GrantMaiden/ContactlessPiPoweredDrumkit/embedded/docs/pdf/files.tex

\doxysubsection{File List}
Here is a list of all documented files with brief descriptions\+:\begin{DoxyCompactList}
\item\contentsline{section}{include/\mbox{\hyperlink{btb__main_8h_source}{btb\+\_\+main.\+h}} }{\pageref{btb__main_8h_source}}{}
\item\contentsline{section}{include/\mbox{\hyperlink{controller_8h_source}{controller.\+h}} }{\pageref{controller_8h_source}}{}
\item\contentsline{section}{include/\mbox{\hyperlink{CppThread_8h_source}{Cpp\+Thread.\+h}} }{\pageref{CppThread_8h_source}}{}
\item\contentsline{section}{include/\mbox{\hyperlink{CppTimer_8h_source}{Cpp\+Timer.\+h}} }{\pageref{CppTimer_8h_source}}{}
\item\contentsline{section}{include/\mbox{\hyperlink{defines_8h_source}{defines.\+h}} }{\pageref{defines_8h_source}}{}
\item\contentsline{section}{include/\mbox{\hyperlink{gpio__controller_8h_source}{gpio\+\_\+controller.\+h}} }{\pageref{gpio__controller_8h_source}}{}
\item\contentsline{section}{include/\mbox{\hyperlink{led_8h_source}{led.\+h}} }{\pageref{led_8h_source}}{}
\item\contentsline{section}{include/\mbox{\hyperlink{platform_8h_source}{platform.\+h}} }{\pageref{platform_8h_source}}{}
\item\contentsline{section}{include/\mbox{\hyperlink{ranging_8h_source}{ranging.\+h}} }{\pageref{ranging_8h_source}}{}
\item\contentsline{section}{include/\mbox{\hyperlink{sound_8h_source}{sound.\+h}} }{\pageref{sound_8h_source}}{}
\item\contentsline{section}{include/\mbox{\hyperlink{types_8h_source}{types.\+h}} }{\pageref{types_8h_source}}{}
\item\contentsline{section}{include/\mbox{\hyperlink{VL53L4CD__api_8h_source}{VL53\+L4\+CD\+\_\+api.\+h}} }{\pageref{VL53L4CD__api_8h_source}}{}
\end{DoxyCompactList}
