GrantMaiden/ContactlessPiPoweredDrumkit/embedded/docs/pdf/hierarchy.tex

\doxysubsection{Class Hierarchy}
This inheritance list is sorted roughly, but not completely, alphabetically\+:\begin{DoxyCompactList}
\item \contentsline{section}{Cpp\+Thread}{\pageref{classCppThread}}{}
\item \contentsline{section}{Cpp\+Timer}{\pageref{classCppTimer}}{}
\begin{DoxyCompactList}
\item \contentsline{section}{Led\+Control}{\pageref{classLedControl}}{}
\end{DoxyCompactList}
\item \contentsline{section}{Gpio\+Controller}{\pageref{classGpioController}}{}
\item \contentsline{section}{Platform\+VL53l4\+CD}{\pageref{classPlatformVL53l4CD}}{}
\item \contentsline{section}{sensor\+Hit}{\pageref{structsensorHit}}{}
\item \contentsline{section}{sensor\+Values}{\pageref{structsensorValues}}{}
\item \contentsline{section}{Sound}{\pageref{classSound}}{}
\item \contentsline{section}{VL53\+L4\+CD}{\pageref{classVL53L4CD}}{}
\begin{DoxyCompactList}
\item \contentsline{section}{Controller}{\pageref{classController}}{}
\end{DoxyCompactList}
\item \contentsline{section}{VL53\+L4\+CD\+\_\+\+API}{\pageref{classVL53L4CD__API}}{}
\item \contentsline{section}{VL53\+L4\+CD\+\_\+\+Linux\+Dev}{\pageref{structVL53L4CD__LinuxDev}}{}
\item \contentsline{section}{VL53\+L4\+CD\+\_\+\+Results\+Data\+\_\+t}{\pageref{structVL53L4CD__ResultsData__t}}{}
\item \contentsline{section}{VL53\+L4\+CD\+\_\+\+Version\+\_\+t}{\pageref{structVL53L4CD__Version__t}}{}
\end{DoxyCompactList}
