GrantMaiden/ContactlessPiPoweredDrumkit/embedded/docs/pdf/structsensorHit.tex

\hypertarget{structsensorHit}{}\doxysubsection{sensor\+Hit Struct Reference}
\label{structsensorHit}\index{sensorHit@{sensorHit}}

{\ttfamily \#include $<$controller.\+h$>$}

\doxysubsubsection{Detailed Description}
sensor\+Value structure contains status and distance value of a sensor 

The documentation for this struct was generated from the following file\+:\begin{DoxyCompactItemize}
\item 
include/controller.\+h\end{DoxyCompactItemize}
