GrantMaiden/ContactlessPiPoweredDrumkit/embedded/docs/pdf/structsensorValues.tex

\hypertarget{structsensorValues}{}\doxysubsection{sensor\+Values Struct Reference}
\label{structsensorValues}\index{sensorValues@{sensorValues}}

{\ttfamily \#include $<$defines.\+h$>$}

\doxysubsubsection{Detailed Description}
\mbox{\hyperlink{structsensorValues}{sensor\+Values}} structure contains status and distance value of a sensor 

The documentation for this struct was generated from the following file\+:\begin{DoxyCompactItemize}
\item 
include/defines.\+h\end{DoxyCompactItemize}
