GrantMaiden/ContactlessPiPoweredDrumkit/embedded/docs/pdf/ranging_8h_source.tex

\hypertarget{ranging_8h_source}{}\doxysubsection{ranging.\+h}
\label{ranging_8h_source}\index{include/ranging.h@{include/ranging.h}}

\begin{DoxyCode}{0}
\DoxyCodeLine{1 \textcolor{comment}{/****************************** Module Header ******************************\(\backslash\)}}
\DoxyCodeLine{2 \textcolor{comment}{Module Name:    ranging.h}}
\DoxyCodeLine{3 \textcolor{comment}{Project:        btb}}
\DoxyCodeLine{4 \textcolor{comment}{Author:         Lucas Zehner}}
\DoxyCodeLine{5 \textcolor{comment}{Description:    contains ranging definitions and headers}}
\DoxyCodeLine{6 \textcolor{comment}{\(\backslash\)***************************************************************************/}}
\DoxyCodeLine{7 \textcolor{preprocessor}{\#ifndef RANGING\_H}}
\DoxyCodeLine{8 \textcolor{preprocessor}{\#define RANGING\_H}}
\DoxyCodeLine{9 \textcolor{keyword}{class }\mbox{\hyperlink{classGpioController}{GpioController}};}
\DoxyCodeLine{10 }
\DoxyCodeLine{11 }
\DoxyCodeLine{12 \textcolor{preprocessor}{\#define VL53L4CD\_I2C\_FAST\_MODE\_PLUS}}
\DoxyCodeLine{13 \textcolor{comment}{// Includes}}
\DoxyCodeLine{14 \textcolor{keyword}{extern} \textcolor{stringliteral}{"{}C"{}} \{}
\DoxyCodeLine{15 }
\DoxyCodeLine{16 \}}
\DoxyCodeLine{17 \textcolor{preprocessor}{\#include "{}VL53L4CD\_api.h"{}}}
\DoxyCodeLine{18 \textcolor{preprocessor}{\#include "{}types.h"{}}}
\DoxyCodeLine{19 \textcolor{preprocessor}{\#include "{}platform.h"{}}}
\DoxyCodeLine{20 \textcolor{preprocessor}{\#include <pigpio.h>}}
\DoxyCodeLine{21 }
\DoxyCodeLine{22 \textcolor{comment}{// Defines}}
\DoxyCodeLine{23 \textcolor{preprocessor}{\#define I2C\_ADDRESS\_INIT    0x52}}
\DoxyCodeLine{24 \textcolor{preprocessor}{\#define D1\_I2C\_ADDRESS      0x52}}
\DoxyCodeLine{25 \textcolor{preprocessor}{\#define D2\_I2C\_ADDRESS      0x54}}
\DoxyCodeLine{26 \textcolor{preprocessor}{\#define D3\_I2C\_ADDRESS      0x56}}
\DoxyCodeLine{27 \textcolor{preprocessor}{\#define D4\_I2C\_ADDRESS      0x58}}
\DoxyCodeLine{28 \textcolor{preprocessor}{\#define D5\_I2C\_ADDRESS      0x60}}
\DoxyCodeLine{29 \textcolor{preprocessor}{\#define D6\_I2C\_ADDRESS      0x62}}
\DoxyCodeLine{30 \textcolor{comment}{// Change these as desired}}
\DoxyCodeLine{31 \textcolor{preprocessor}{\#define RANGE\_TIMING\_MAX    10}}
\DoxyCodeLine{32 \textcolor{preprocessor}{\#define RANGING\_LIM\_LOW     10}}
\DoxyCodeLine{33 \textcolor{preprocessor}{\#define RANGING\_LIM\_HIGH    500}}
\DoxyCodeLine{34 }
\DoxyCodeLine{35 \textcolor{keyword}{using namespace }std;}
\DoxyCodeLine{36 \textcolor{keyword}{class }\mbox{\hyperlink{classVL53L4CD}{VL53L4CD}}}
\DoxyCodeLine{37 \{}
\DoxyCodeLine{38     \textcolor{keyword}{public}:}
\DoxyCodeLine{39         \textcolor{comment}{//Functions}}
\DoxyCodeLine{40 }
\DoxyCodeLine{44         \textcolor{keywordtype}{void} \mbox{\hyperlink{classVL53L4CD_aa50845e779bebe4d312e79ef1a14a62b}{rangingInit}}();}
\DoxyCodeLine{45 }
\DoxyCodeLine{49         \textcolor{keywordtype}{void} \mbox{\hyperlink{classVL53L4CD_a07ac79dcf2d0ba4c91df4fb0aea824f0}{rangingTestDistanceSensors}}();}
\DoxyCodeLine{50 }
\DoxyCodeLine{56         \mbox{\hyperlink{structsensorValues}{sensorValues}} \mbox{\hyperlink{classVL53L4CD_ad81309cbabd2f3a7f4eb1c26cd97a64d}{rangingGetData}}(sensorID sensor);}
\DoxyCodeLine{57 }
\DoxyCodeLine{63         \textcolor{keywordtype}{bool} \mbox{\hyperlink{classVL53L4CD_af33c4ab62ad9db0773ed3dadaa0257c5}{rangingCheckIfReady}}(sensorID sensor);}
\DoxyCodeLine{64 }
\DoxyCodeLine{72         \textcolor{keyword}{virtual} \textcolor{keywordtype}{void} \mbox{\hyperlink{classVL53L4CD_a149a2250aabe18254a50be683b9fbba5}{distanceDataReady}}(\mbox{\hyperlink{structsensorValues}{sensorValues}} sensVals, sensorID sensor) = 0;}
\DoxyCodeLine{73 }
\DoxyCodeLine{74     \textcolor{keyword}{private}:}
\DoxyCodeLine{75         \textcolor{comment}{// private global variables}}
\DoxyCodeLine{76         \mbox{\hyperlink{structVL53L4CD__LinuxDev}{VL53L4CD\_LinuxDev}} linuxDev1;}
\DoxyCodeLine{77         \mbox{\hyperlink{structVL53L4CD__LinuxDev}{Dev\_t}} i2cdev\_Sensor1 = \&linuxDev1;}
\DoxyCodeLine{78         \mbox{\hyperlink{structVL53L4CD__LinuxDev}{VL53L4CD\_LinuxDev}} linuxDev2;}
\DoxyCodeLine{79         \mbox{\hyperlink{structVL53L4CD__LinuxDev}{Dev\_t}} i2cdev\_Sensor2 = \&linuxDev2;}
\DoxyCodeLine{80         \mbox{\hyperlink{structVL53L4CD__LinuxDev}{VL53L4CD\_LinuxDev}} linuxDev3;}
\DoxyCodeLine{81         \mbox{\hyperlink{structVL53L4CD__LinuxDev}{Dev\_t}} i2cdev\_Sensor3 = \&linuxDev3;}
\DoxyCodeLine{82         \mbox{\hyperlink{structVL53L4CD__LinuxDev}{VL53L4CD\_LinuxDev}} linuxDev4;}
\DoxyCodeLine{83         \mbox{\hyperlink{structVL53L4CD__LinuxDev}{Dev\_t}} i2cdev\_Sensor4 = \&linuxDev4;}
\DoxyCodeLine{84         \mbox{\hyperlink{structVL53L4CD__LinuxDev}{VL53L4CD\_LinuxDev}} linuxDev5;}
\DoxyCodeLine{85         \mbox{\hyperlink{structVL53L4CD__LinuxDev}{Dev\_t}} i2cdev\_Sensor5 = \&linuxDev5;}
\DoxyCodeLine{86         \mbox{\hyperlink{structVL53L4CD__LinuxDev}{VL53L4CD\_LinuxDev}} linuxDev6;}
\DoxyCodeLine{87         \mbox{\hyperlink{structVL53L4CD__LinuxDev}{Dev\_t}} i2cdev\_Sensor6 = \&linuxDev6;}
\DoxyCodeLine{88 }
\DoxyCodeLine{89 }
\DoxyCodeLine{94         \textcolor{keywordtype}{void} rangingInitDistanceSensor(\textcolor{keywordtype}{int} \textcolor{keywordtype}{id}, \mbox{\hyperlink{structVL53L4CD__LinuxDev}{Dev\_t}} dev);}
\DoxyCodeLine{95 }
\DoxyCodeLine{101         \textcolor{keywordtype}{bool} rangingSetXshut(\textcolor{keywordtype}{int} \textcolor{keywordtype}{id});}
\DoxyCodeLine{102 }
\DoxyCodeLine{108         \textcolor{keywordtype}{void} rangingChangeAddress(\mbox{\hyperlink{structVL53L4CD__LinuxDev}{Dev\_t}} dev, \textcolor{keywordtype}{int} \textcolor{keywordtype}{id});}
\DoxyCodeLine{109 }
\DoxyCodeLine{113         \textcolor{keywordtype}{void} rangingPollingTestAll();}
\DoxyCodeLine{114 }
\DoxyCodeLine{115         \textcolor{keywordtype}{void} dataReadyISR(\textcolor{keywordtype}{int} gpio);}
\DoxyCodeLine{116 }
\DoxyCodeLine{117         \textcolor{keyword}{static} \textcolor{keywordtype}{void} rangingISRCallback(\textcolor{keywordtype}{int} gpio, \textcolor{keywordtype}{int}, uint32\_t, \textcolor{keywordtype}{void}* userdata) \{}
\DoxyCodeLine{118             ((\mbox{\hyperlink{classVL53L4CD}{VL53L4CD}}*)userdata)-\/>dataReadyISR(gpio);}
\DoxyCodeLine{119         \}}
\DoxyCodeLine{120 }
\DoxyCodeLine{121 }
\DoxyCodeLine{122 \};}
\DoxyCodeLine{123 }
\DoxyCodeLine{124 }
\DoxyCodeLine{125 \textcolor{preprocessor}{\#endif }\textcolor{comment}{// RANGING\_H}}
\DoxyCodeLine{126 }
\DoxyCodeLine{127 }
\DoxyCodeLine{128 }
\DoxyCodeLine{129 }
\DoxyCodeLine{130 }
\DoxyCodeLine{131 }
\DoxyCodeLine{132 }
\DoxyCodeLine{133 }
\DoxyCodeLine{134 }
\DoxyCodeLine{135 }

\end{DoxyCode}
