GrantMaiden/ContactlessPiPoweredDrumkit/embedded/docs/pdf/refman.tex

  % Handle batch mode
  % to overcome problems with too many open files
  \let\mypdfximage\pdfximage\def\pdfximage{\immediate\mypdfximage}
  % Set document class depending on configuration
  \documentclass[twoside]{article}
  %% moved from doxygen.sty due to workaround for LaTex 2019 version and unmaintained tabu package
  \usepackage{ifthen}
  \ifx\requestedLaTeXdate\undefined
    \usepackage{array}
  \else
    \usepackage{array}[=2016-10-06]
  \fi
  %%
  % Packages required by doxygen
  \usepackage{fixltx2e} % for \textsubscript
  \usepackage{doxygen}
  \usepackage{graphicx}
  \usepackage[utf8]{inputenc}
  \usepackage{makeidx}
  \PassOptionsToPackage{warn}{textcomp}
  \usepackage{textcomp}
  \usepackage[nointegrals]{wasysym}
  \usepackage{ifxetex}
  % NLS support packages
  % Define default fonts
  % Font selection
  \usepackage[T1]{fontenc}
  % set main and monospaced font
  \usepackage[scaled=.90]{helvet}
\usepackage{courier}
\renewcommand{\familydefault}{\sfdefault}
  \usepackage{sectsty}
  \allsectionsfont{%
    \fontseries{bc}\selectfont%
    \color{darkgray}%
  }
  \renewcommand{\DoxyLabelFont}{%
    \fontseries{bc}\selectfont%
    \color{darkgray}%
  }
  \newcommand{\+}{\discretionary{\mbox{\scriptsize$\hookleftarrow$}}{}{}}
   % Arguments of doxygenemoji:
   % 1) ':<text>:' form of the emoji, already LaTeX-escaped
   % 2) file with the name of the emoji without the .png extension
   % in case image exist use this otherwise use the ':<text>:' form
   \newcommand{\doxygenemoji}[2]{%
     \IfFileExists{./#2.png}{\raisebox{-0.1em}{}}{#1}%
   }
  % Page & text layout
  \usepackage{geometry}
  \geometry{%
    a4paper,%
    top=2.5cm,%
    bottom=2.5cm,%
    left=2.5cm,%
    right=2.5cm%
  }
  % Allow a bit of overflow to go unnoticed by other means
  \tolerance=750
  \hfuzz=15pt
  \hbadness=750
  \setlength{\emergencystretch}{15pt}
  \setlength{\parindent}{0cm}
  \newcommand{\doxynormalparskip}{\setlength{\parskip}{3ex plus 2ex minus 2ex}}
  \newcommand{\doxytocparskip}{\setlength{\parskip}{1ex plus 0ex minus 0ex}}
  \doxynormalparskip
  % Redefine paragraph/subparagraph environments, using sectsty fonts
  \makeatletter
  \renewcommand{\paragraph}{%
    \@startsection{paragraph}{4}{0ex}{-1.0ex}{1.0ex}{%
      \normalfont\normalsize\bfseries\SS@parafont%
    }%
  }
  \renewcommand{\subparagraph}{%
    \@startsection{subparagraph}{5}{0ex}{-1.0ex}{1.0ex}{%
      \normalfont\normalsize\bfseries\SS@subparafont%
    }%
  }
  \makeatother
  \makeatletter
  \newcommand\hrulefilll{\leavevmode\leaders\hrule\hskip 0pt plus 1filll\kern\z@}
  \makeatother
  % Headers & footers
  \usepackage{fancyhdr}
  \pagestyle{fancyplain}
  \renewcommand{\footrulewidth}{0.4pt}
  \fancypagestyle{fancyplain}{
    \fancyhf{}
    \fancyhead[LE, RO]{\bfseries\thepage}
    \fancyhead[LO]{\bfseries\rightmark}
    \fancyhead[RE]{\bfseries\leftmark}
    \fancyfoot[LO, RE]{\bfseries\scriptsize Generated by Doxygen }
  }
  \fancypagestyle{plain}{
    \fancyhf{}
    \fancyfoot[LO, RE]{\bfseries\scriptsize Generated by Doxygen }
    \renewcommand{\headrulewidth}{0pt}
  }
  \pagestyle{fancyplain}
  \renewcommand{\sectionmark}[1]{%
    \markright{\thesection\ #1}%
  }
  % ToC, LoF, LoT, bibliography, and index
  % Indices & bibliography
  \usepackage{natbib}
  \usepackage[titles]{tocloft}
  \setcounter{tocdepth}{3}
  \setcounter{secnumdepth}{5}
  % creating indexes
  \makeindex
  \usepackage{newunicodechar}
  \newunicodechar{⁻}{${}^{-}$}% Superscript minus
  \newunicodechar{²}{${}^{2}$}% Superscript two
  \newunicodechar{³}{${}^{3}$}% Superscript three
  % Hyperlinks
    % Hyperlinks (required, but should be loaded last)
    \ifpdf
      \usepackage[pdftex,pagebackref=true]{hyperref}
    \else
      \ifxetex
        \usepackage[pagebackref=true]{hyperref}
      \else
        \usepackage[ps2pdf,pagebackref=true]{hyperref}
      \fi
    \fi
    \hypersetup{%
      colorlinks=true,%
      linkcolor=blue,%
      citecolor=blue,%
      unicode,%
      pdftitle={btb},%
      pdfsubject={}%
    }
  % Custom commands used by the header
  % Custom commands
  \newcommand{\clearemptydoublepage}{%
    \newpage{\pagestyle{empty}\cleardoublepage}%
  }
  % caption style definition
  \usepackage{caption}
  \captionsetup{labelsep=space,justification=centering,font={bf},singlelinecheck=off,skip=4pt,position=top}
  % in page table of contents
  \usepackage{etoc}
  \etocsettocstyle{\doxytocparskip}{\doxynormalparskip}
  % prevent numbers overlap the titles in toc
  \renewcommand{\numberline}[1]{#1~}
% End of preamble, now comes the document contents
%===== C O N T E N T S =====
\begin{document}
  \raggedbottom
  % Titlepage & ToC
    % To avoid duplicate page anchors due to reuse of same numbers for
    % the index (be it as roman numbers)
    \hypersetup{pageanchor=false,
                bookmarksnumbered=true,
                pdfencoding=unicode
               }
  \pagenumbering{alph}
  \begin{titlepage}
  \vspace*{7cm}
  \begin{center}%
  {\Large btb}\\
  \vspace*{1cm}
  {\large Generated by Doxygen 1.9.4}\\
  \end{center}
  \end{titlepage}
  \pagenumbering{roman}
  \tableofcontents
  \pagenumbering{arabic}
  % re-enable anchors again
  \hypersetup{pageanchor=true}
%--- Begin generated contents ---
\doxysection{Hierarchical Index}
\input{hierarchy}
\doxysection{Class Index}
\input{annotated}
\doxysection{File Index}
\input{files}
\doxysection{Class Documentation}
\input{classController}
\input{classCppThread}
\input{classCppTimer}
\input{classGpioController}
\input{classLedControl}
\input{classPlatformVL53l4CD}
\input{structsensorHit}
\input{structsensorValues}
\input{classSound}
\input{classVL53L4CD}
\input{classVL53L4CD__API}
\input{structVL53L4CD__LinuxDev}
\input{structVL53L4CD__ResultsData__t}
\input{structVL53L4CD__Version__t}
\doxysection{File Documentation}
\input{btb__main_8h_source}
\input{controller_8h_source}
\input{CppThread_8h_source}
\input{CppTimer_8h_source}
\input{defines_8h_source}
\input{gpio__controller_8h_source}
\input{led_8h_source}
\input{platform_8h_source}
\input{ranging_8h_source}
\input{sound_8h_source}
\input{types_8h_source}
\input{VL53L4CD__api_8h_source}
%--- End generated contents ---
% Index
  \newpage
  \phantomsection
  \clearemptydoublepage
  \addcontentsline{toc}{section}{\indexname}
  \printindex
% Required for some languages (in combination with latexdocumentpre from the header)
\end{document}
