GrantMaiden/ContactlessPiPoweredDrumkit/docs/Sensor_data_example.png

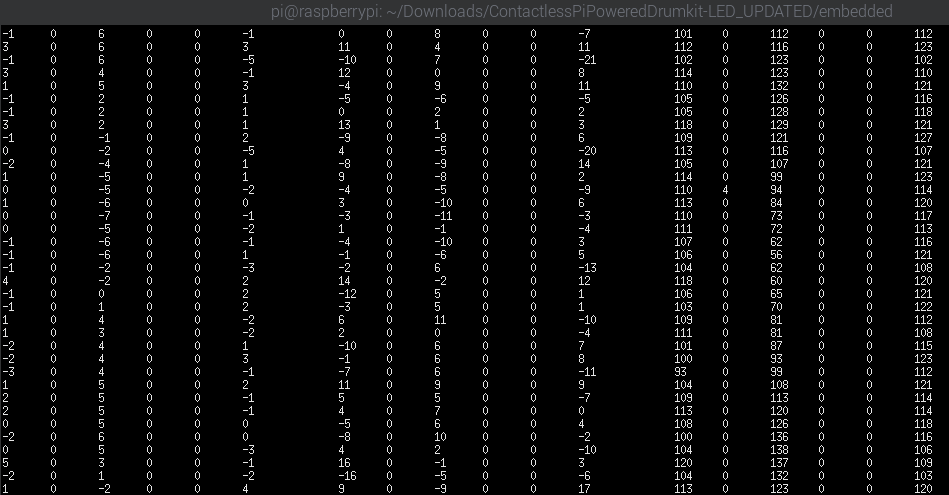
docs/Sensor_data_example.png
